HolyErgo/likeeb/pcbs/edited/left_thumbs_rev1.2.kicad_pcb

## KiCad design pcbs/edited/left_thumbs_rev1.2.kicad_pcb (2023-08-26, an earlier design)

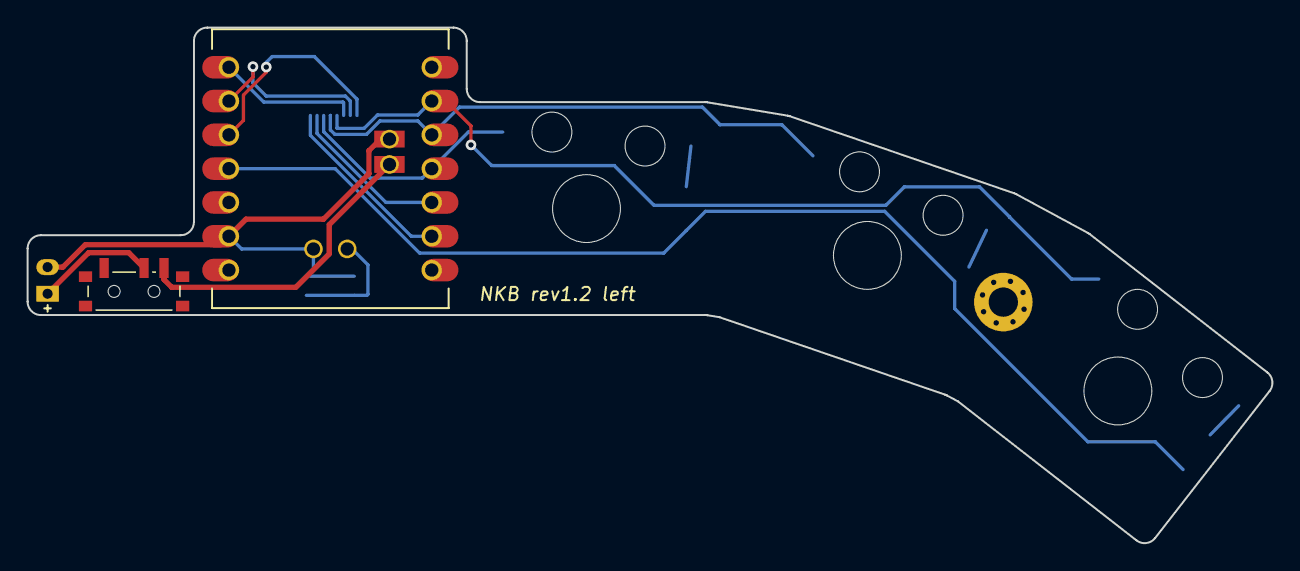
[picture p22: board left_thumbs_rev1.2.kicad_pcb from above]

Board: 2 copper layers, 93.5 x 38.7 mm, 8 parts (1 on the bottom side), 5 nets.

Parts:
BAT1: BatteryPad
S1, S2, S3: GateronLowProfileSwitch
SW1: power_switch
SW2: sw_reset_side
_2: HKWClamshellSocket
_3: MountingHole_2.2mm_M2_Pad_Via

Connections:
BAT_P: BAT1.1, SW1.2
CT3: S1.1, _2.3
CT4: S2.1, _2.4
CT5: S3.1, _2.5
GND: BAT1.2, SW2.1
