HolyErgo/likeeb/pcbs/edited/matrix_pcb_rev1.kicad_pcb

## KiCad design pcbs/edited/matrix_pcb_rev1.kicad_pcb (2023-08-26, an earlier design)

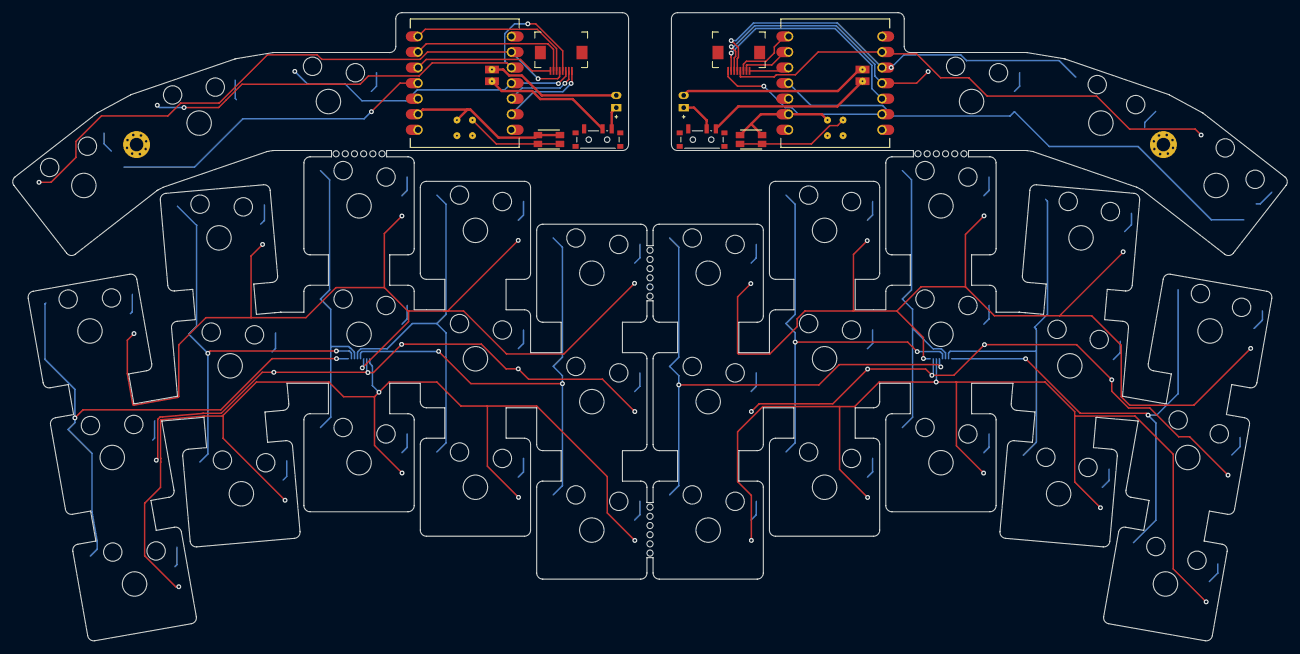
[picture p23: board matrix_pcb_rev1.kicad_pcb from above]

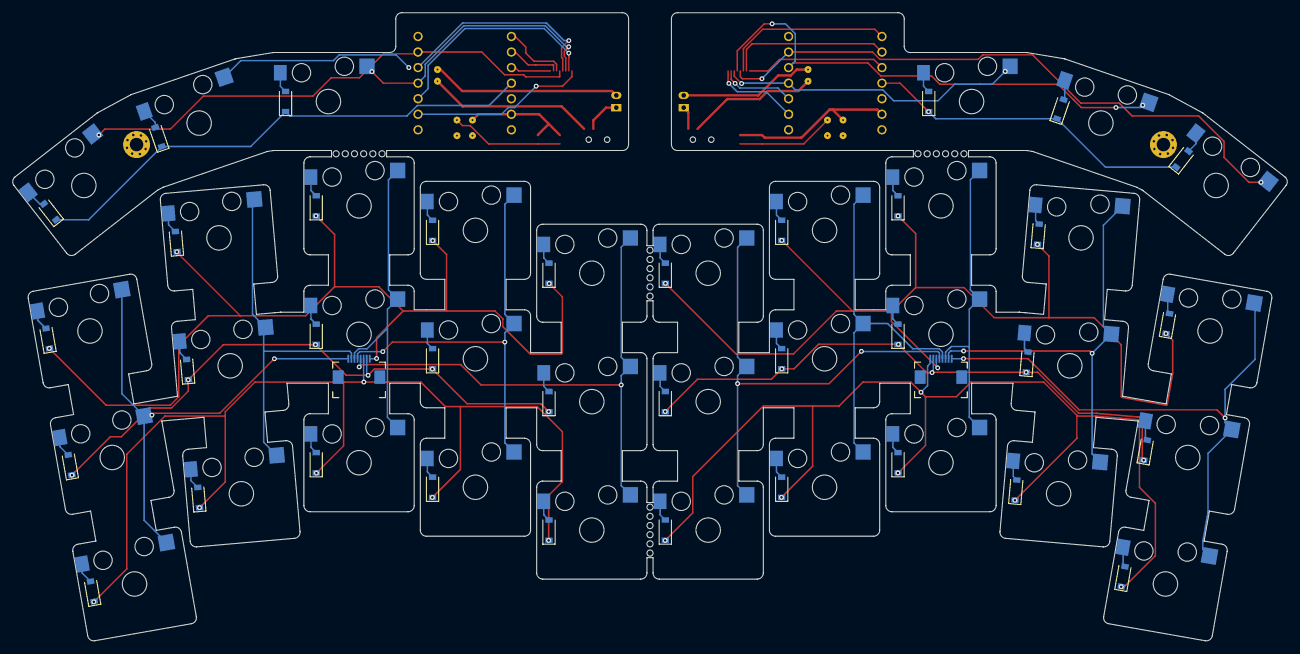
[picture p24: board matrix_pcb_rev1.kicad_pcb from below]

Board: 2 copper layers, 208.1 x 102.5 mm, 88 parts (38 on the bottom side), 62 nets.

Parts:
BAT1, BAT2: BatteryPad
D1, D2, D3, D4, D5, D6, D7, D8, D9, D10, D11, D12, D13, D14, D15, D16, D17, D18, D19, D20, D21, D22, D23, D24, D25, D26, D27, D28, D29, D30, D31, D32, D33, D34, D35, D36: SmdDiode
S1, S2, S3, S4, S5, S6, S7, S8, S9, S10, S11, S12, S13, S14, S15, S16, S17, S18, S19, S20, S21, S22, S23, S24, S25, S26, S27, S28, S29, S30, S31, S32, S33, S34, S35, S36: MX
SW1, SW3: power_switch
SW2, SW4: sw_reset_side
_1, _3, _5, _7: HKWClamshellSocket
_4, _8: MountingHole_2.2mm_M2_Pad_Via
_9, _10, _11, _12: Bridge holes 6 x 1mm

Connections:
BAT_P: BAT1.1, SW1.2
C1: S1.1, S2.1, S3.1, _1.8
C2: S4.1, S5.1, S6.1, _1.7
C3: S7.1, S8.1, S9.1, _1.6
C4: S10.1, S11.1, S12.1, _1.5
C5: S13.1, S14.1, S15.1, _1.4
C6: S28.1, S29.1, S30.1, _5.5
C7: S25.1, S26.1, S27.1, _5.4
C8: S22.1, S23.1, S24.1, _5.3
C9: S19.1, S20.1, S21.1, _5.2
C10: S16.1, S17.1, S18.1, _5.1
CT3: S31.1, _3.3
CT4: S32.1, _3.4
CT5: S33.1, _3.5
CT6: S36.1, _7.4
CT7: S35.1, _7.5
CT8: S34.1, _7.6
RBAT_P: BAT2.1, SW3.3
RL1: D2.1, D5.1, D8.1, D11.1, D14.1, _1.3
RL2: D1.1, D4.1, D7.1, D10.1, D13.1, _1.2
RL3: D3.1, D6.1, D9.1, D12.1, D15.1, _1.1
RLT4: D31.1, D32.1, D33.1
RR1: D17.1, D20.1, D23.1, D26.1, D29.1, _5.8
RR2: D16.1, D19.1, D22.1, D25.1, D28.1, _5.7
RR3: D18.1, D21.1, D24.1, D27.1, D30.1, _5.6
RRT4: D34.1, D35.1, D36.1
far_only: D33.2, S33.2
home_only: D32.2, S32.2
index_bottom: D12.2, S12.2
index_home: D10.2, S10.2
index_top: D11.2, S11.2
inner_bottom: D15.2, S15.2
inner_home: D13.2, S13.2
inner_top: D14.2, S14.2
middle_bottom: D9.2, S9.2
middle_home: D7.2, S7.2
middle_top: D8.2, S8.2
mirror_far_only: D36.2, S36.2
mirror_home_only: D35.2, S35.2
mirror_index_bottom: D27.2, S27.2
mirror_index_home: D25.2, S25.2
mirror_index_top: D26.2, S26.2
mirror_inner_bottom: D30.2, S30.2
mirror_inner_home: D28.2, S28.2
mirror_inner_top: D29.2, S29.2
mirror_middle_bottom: D24.2, S24.2
mirror_middle_home: D22.2, S22.2
mirror_middle_top: D23.2, S23.2
mirror_near_only: D34.2, S34.2
mirror_pinky_bottom: D18.2, S18.2
mirror_pinky_home: D16.2, S16.2
mirror_pinky_top: D17.2, S17.2
mirror_ring_bottom: D21.2, S21.2
mirror_ring_home: D19.2, S19.2
mirror_ring_top: D20.2, S20.2
near_only: D31.2, S31.2
pinky_bottom: D3.2, S3.2
pinky_home: D1.2, S1.2
pinky_top: D2.2, S2.2
ring_bottom: D6.2, S6.2
ring_home: D4.2, S4.2
ring_top: D5.2, S5.2
